project-neon/NoFollow/Mechanics/STLFiles/Battery_Support.stl

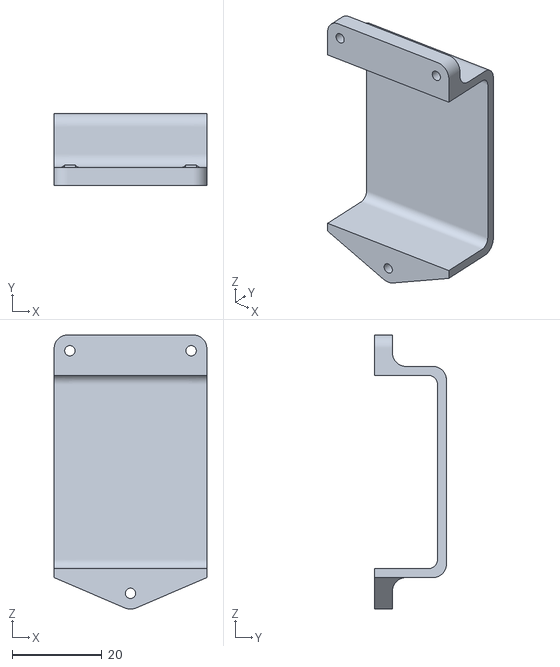
[picture p16: CAD file, 2016-08-27]
Mechanics/STLFiles/Battery_Support.stl
34.0 x 16.0 x 61.0
