project-neon/NoFollow/Mechanics/STLFiles/Sensor_Arm.stl

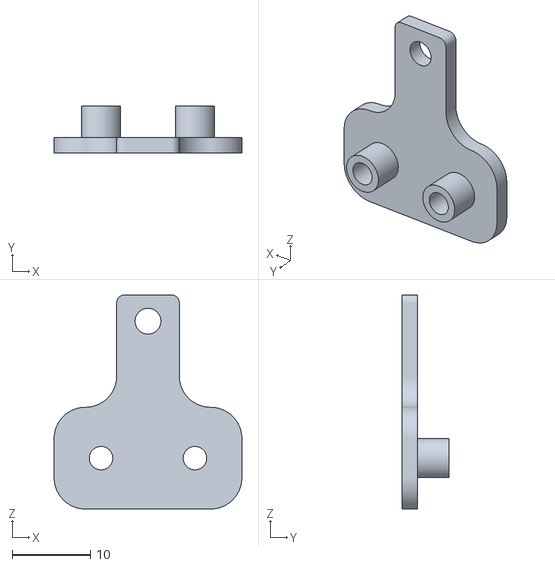
[picture p17: CAD file, 2016-08-27]
Mechanics/STLFiles/Sensor_Arm.stl
24.0 x 6.00 x 27.4
