project-neon/NoFollow/Mechanics/STLFiles/Direction_Bar_Left.stl

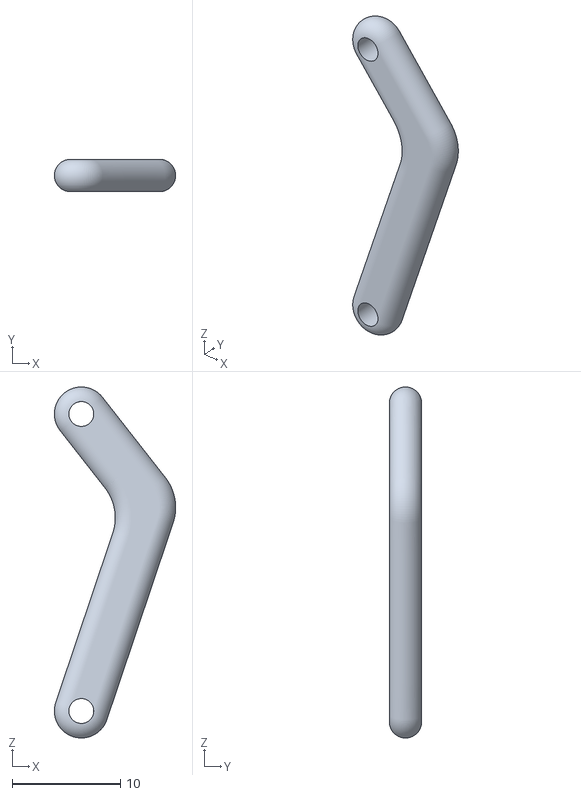
[picture p18: CAD file, 2016-08-27]
Mechanics/STLFiles/Direction_Bar_Left.stl
11.2 x 3.00 x 32.5
