project-neon/NoFollow/Mechanics/STLFiles/Zippy_Lipo_1300mAh.stl

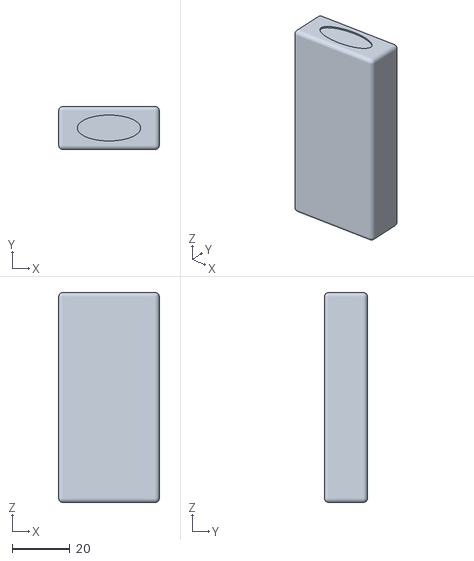
[picture p19: CAD file, 2016-08-27]
Mechanics/STLFiles/Zippy_Lipo_1300mAh.stl
35.0 x 15.0 x 73.0
