project-neon/NoFollow/Mechanics/STLFiles/Rear_Wheel_Cube.stl

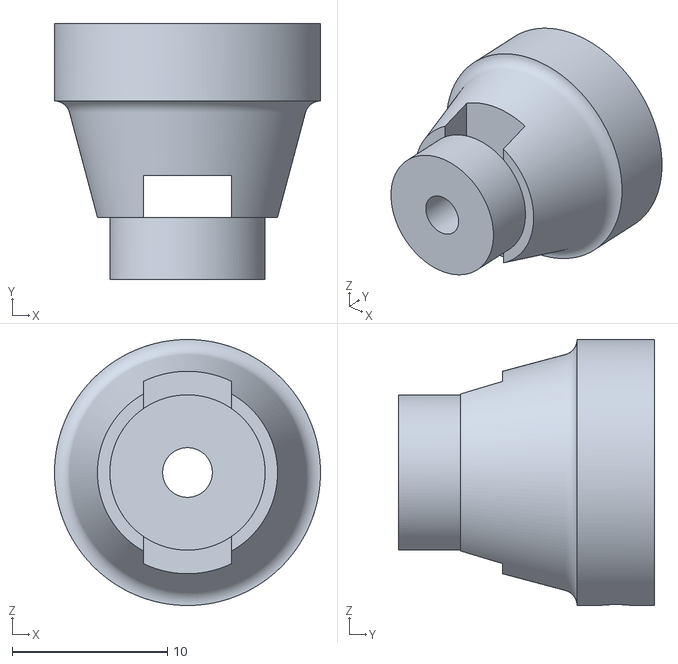
[picture p20: CAD file, 2016-08-27]
Mechanics/STLFiles/Rear_Wheel_Cube.stl
17.1 x 16.5 x 17.1
