project-neon/NoFollow/Mechanics/STLFiles/ServoTGY-306GV2.2.stl

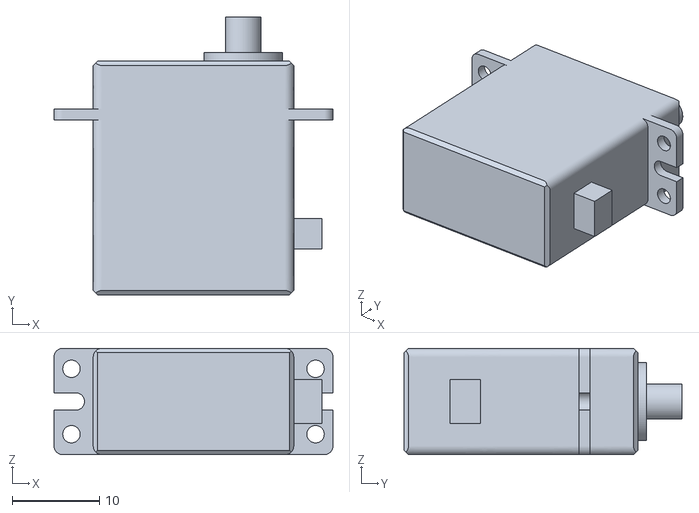
[picture p21: CAD file, 2016-08-27]
Mechanics/STLFiles/ServoTGY-306GV2.2.stl
32.0 x 31.9 x 12.2
