project-neon/NoFollow/Mechanics/STLFiles/Allen_M3x10.stl

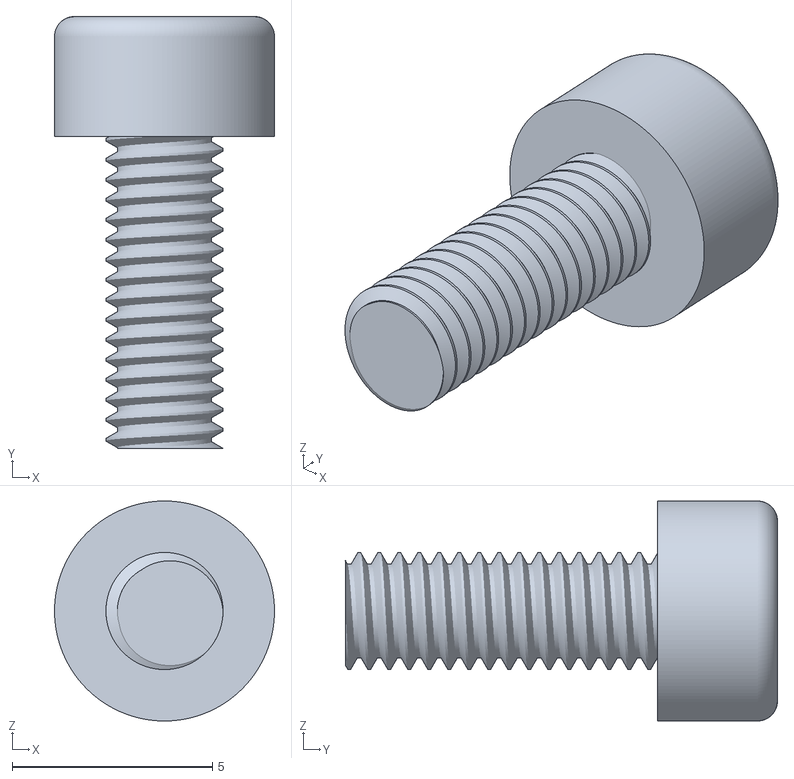
[picture p22: CAD file, 2016-08-27]
Mechanics/STLFiles/Allen_M3x10.stl
5.50 x 10.8 x 5.50
