project-neon/NoFollow/Mechanics/STLFiles/Micro_Gear_Motor_Extended_30-1_With_Bracket.stl

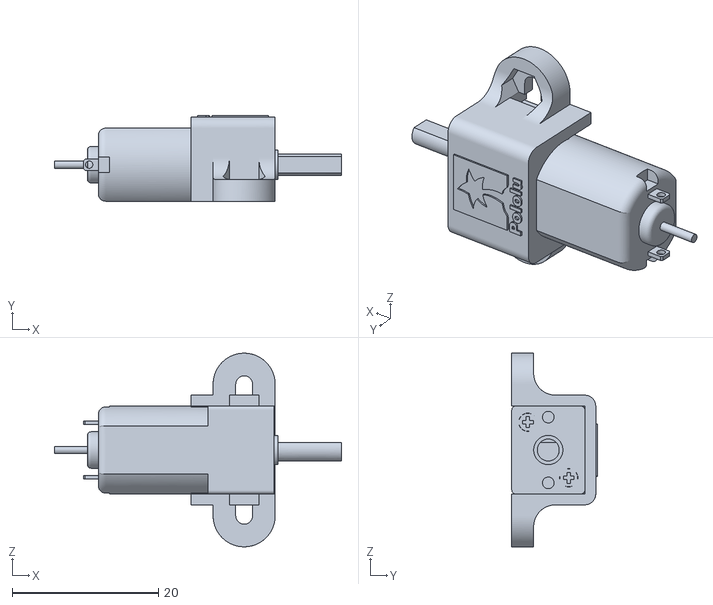
[picture p23: CAD file, 2016-08-27]
Mechanics/STLFiles/Micro_Gear_Motor_Extended_30-1_With_Bracket.stl
39.3 x 11.7 x 26.5
