project-neon/NoFollow/Mechanics/STLFiles/Allen_M2x10.stl

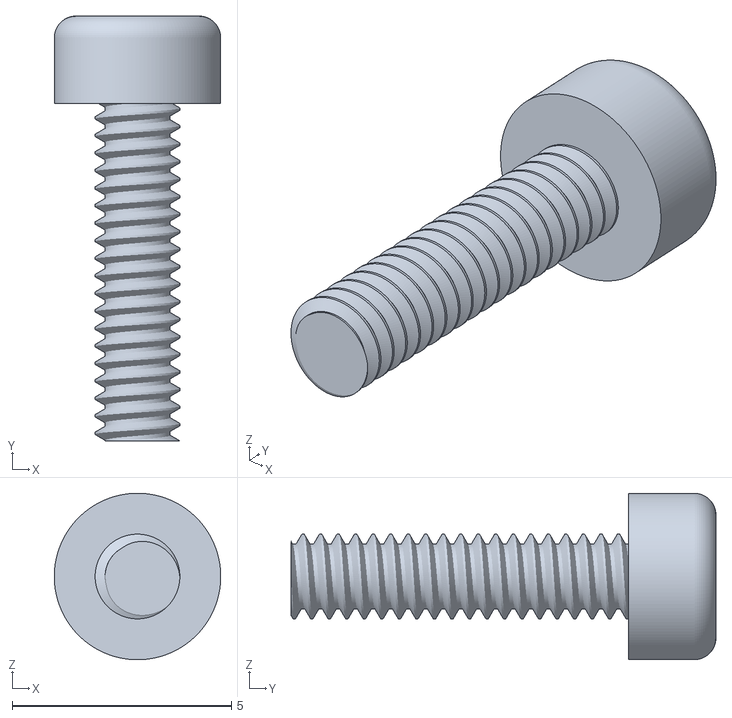
[picture p24: CAD file, 2016-08-27]
Mechanics/STLFiles/Allen_M2x10.stl
3.80 x 9.70 x 3.80
